Jorgehsm/SCARA_arm/robot_arm_cad/montagem_end_effector.SLDASM

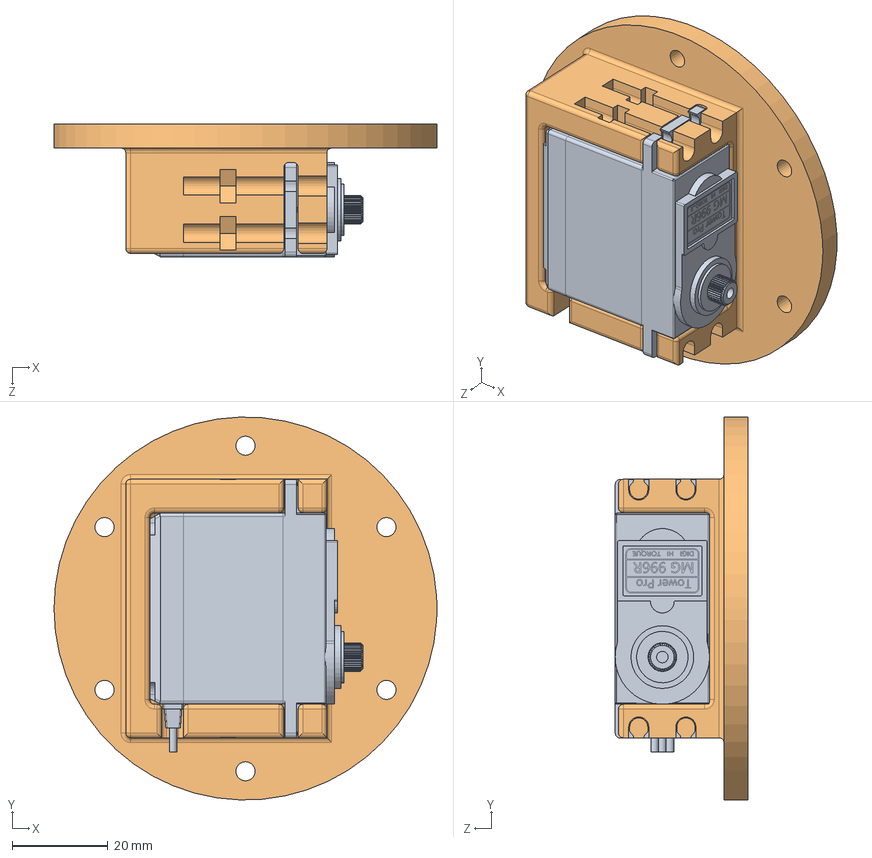
[picture p2: CAD file, 2024-11-08]
robot_arm_cad/montagem_end_effector.SLDASM
80.0 x 80.0 x 27.7 mm
junta_4_servo
servoMotorMG996R
