Jorgehsm/SCARA_arm/robot_arm_cad/garra/attachmentStraight.SLDPRT

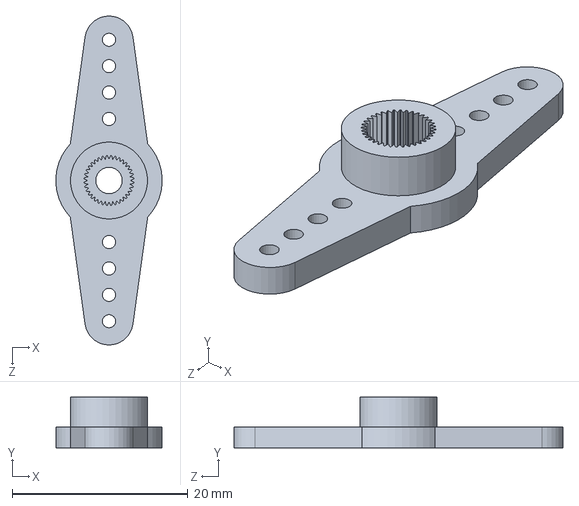
[picture p16: CAD file, 2024-09-22]
robot_arm_cad/garra/attachmentStraight.SLDPRT
12.1 x 5.75 x 37.4 mm
