Jorgehsm/SCARA_arm/robot_arm_cad/ligacao_base_eixoZ.SLDPRT

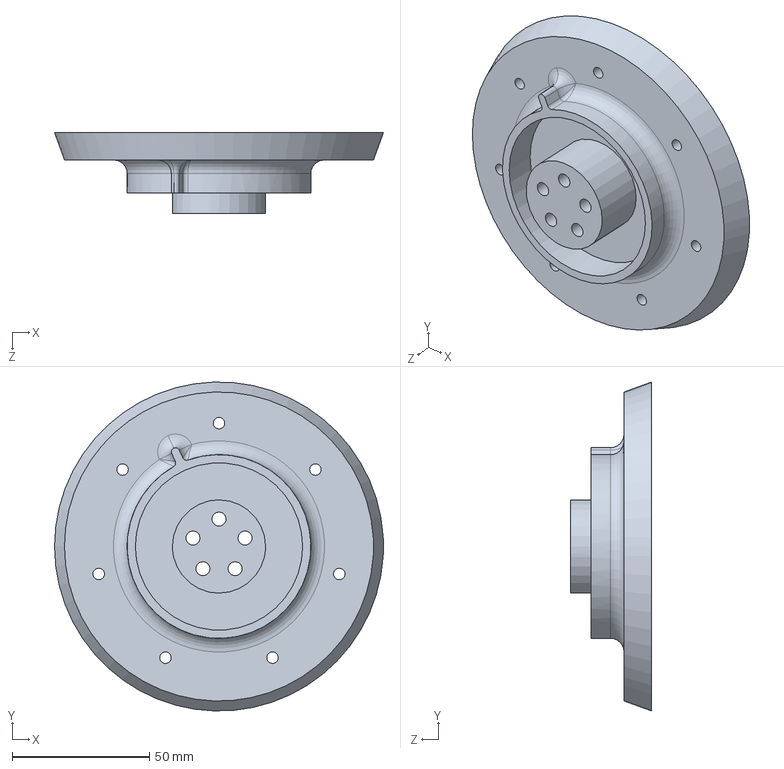
[picture p17: CAD file, 2024-09-22]
robot_arm_cad/ligacao_base_eixoZ.SLDPRT
120.0 x 119.9 x 29.5 mm
