Jorgehsm/SCARA_arm/robot_arm_cad/braco_1.SLDPRT

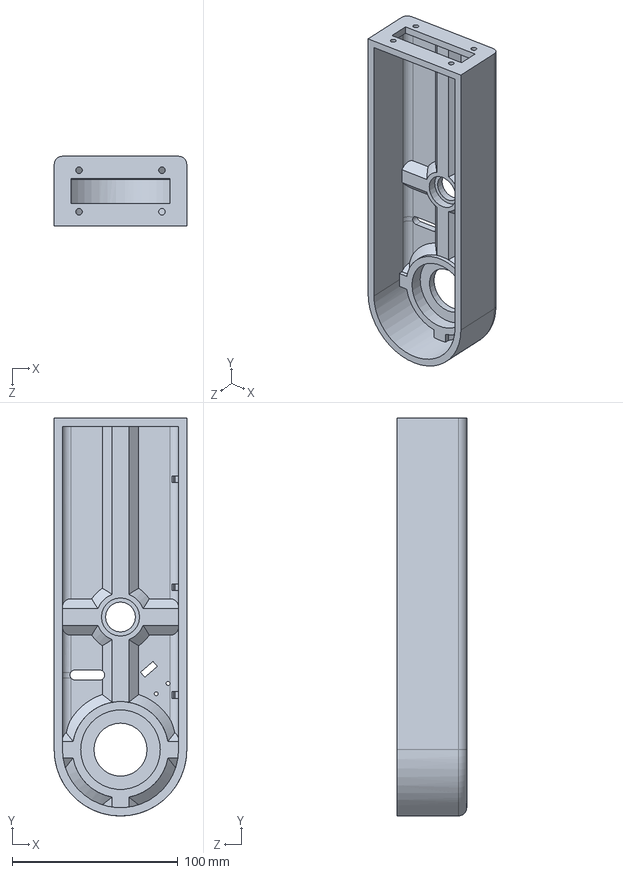
[picture p18: CAD file, 2024-09-22]
robot_arm_cad/braco_1.SLDPRT
80.0 x 240.0 x 42.0 mm
