Jorgehsm/SCARA_arm/robot_arm_cad/garra/presa.SLDPRT

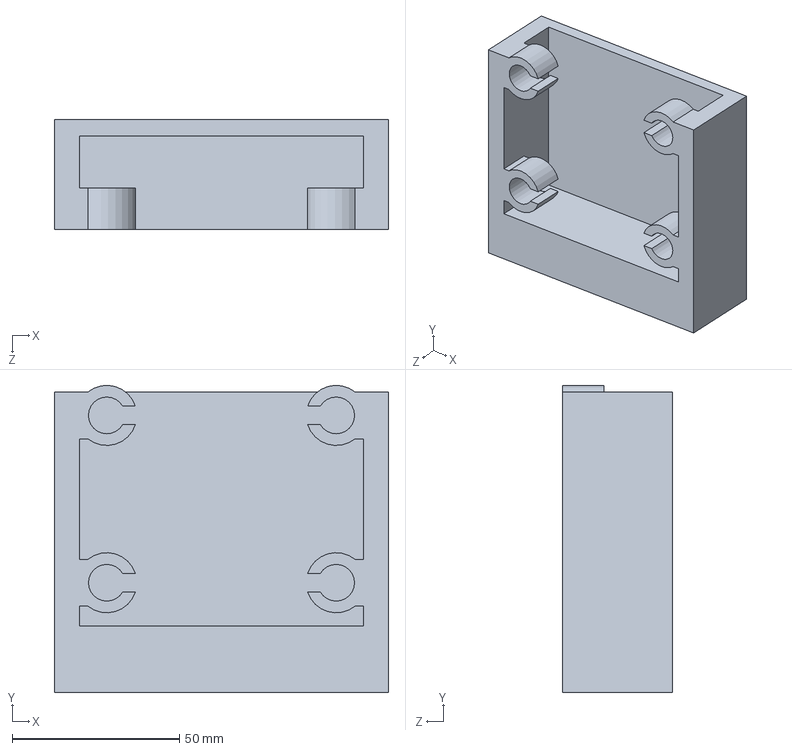
[picture p19: CAD file, 2024-09-22]
robot_arm_cad/garra/presa.SLDPRT
100.0 x 92.0 x 33.0 mm
