Jorgehsm/SCARA_arm/robot_arm_cad/garra/garra_corpo_2.SLDPRT

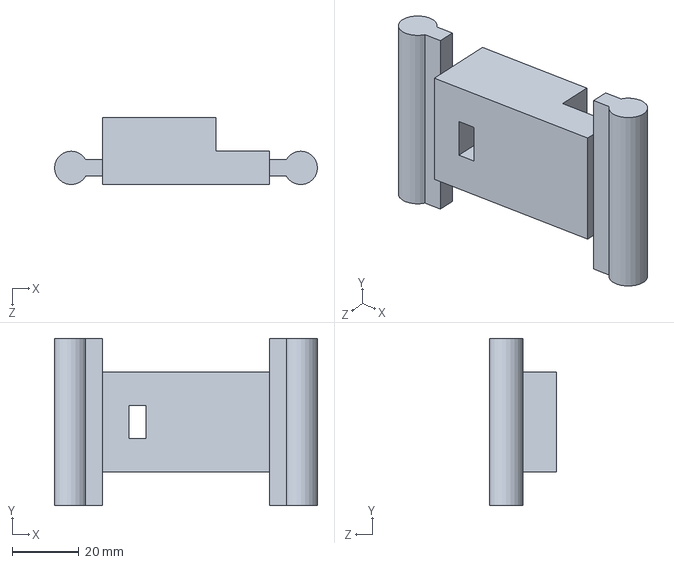
[picture p20: CAD file, 2024-09-22]
robot_arm_cad/garra/garra_corpo_2.SLDPRT
78.7 x 50.0 x 20.1 mm
