Jorgehsm/SCARA_arm/robot_arm_cad/servoMotorMG996R.SLDPRT

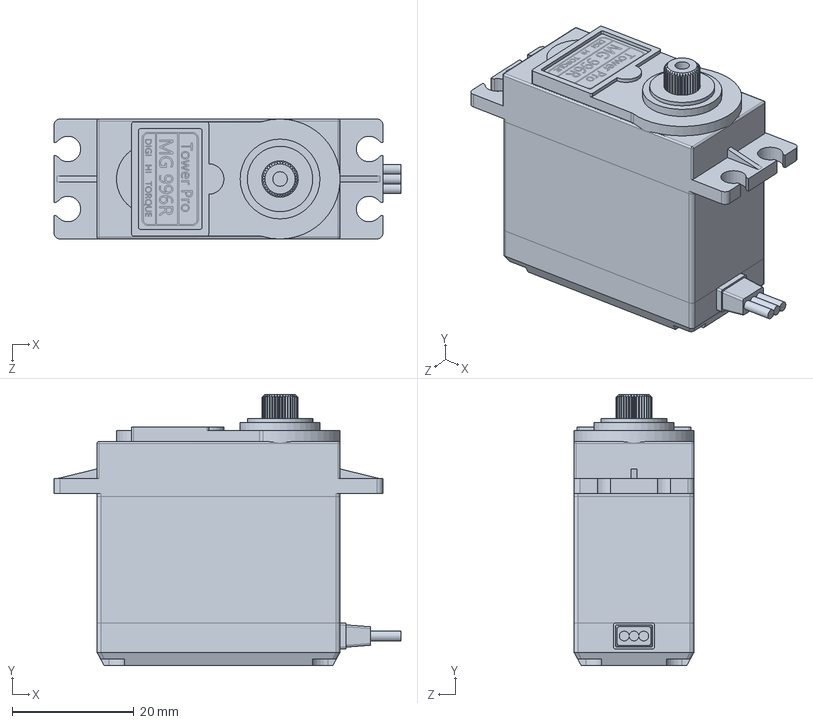
[picture p21: CAD file, 2024-09-22]
robot_arm_cad/servoMotorMG996R.SLDPRT
57.0 x 44.5 x 19.7 mm
