Jorgehsm/SCARA_arm/robot_arm_cad/suporte_eixoZ_superior.SLDPRT

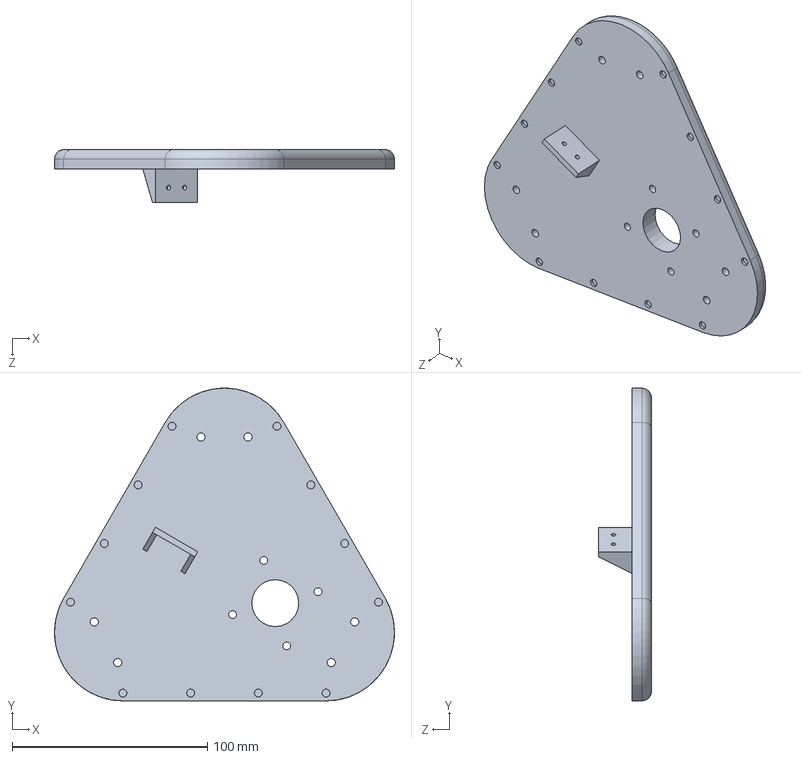
[picture p22: CAD file, 2024-09-22]
robot_arm_cad/suporte_eixoZ_superior.SLDPRT
173.9 x 160.0 x 27.2 mm
