Jorgehsm/SCARA_arm/robot_arm_cad/braco_2.SLDPRT

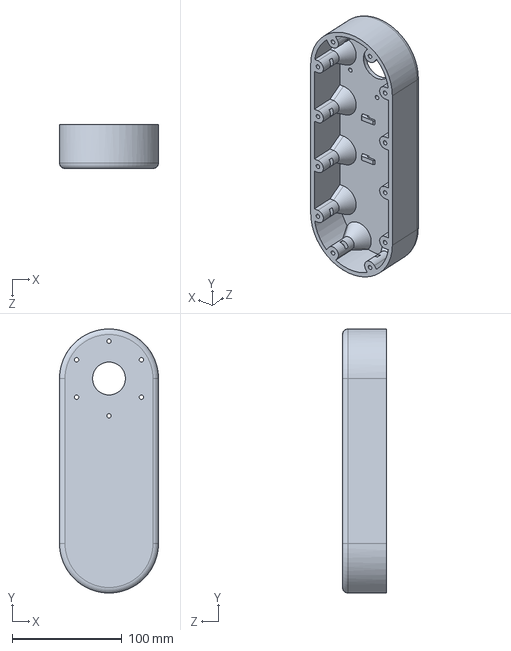
[picture p23: CAD file, 2024-09-22]
robot_arm_cad/braco_2.SLDPRT
90.0 x 240.0 x 40.0 mm
