Jorgehsm/SCARA_arm/robot_arm_cad/castanha_TR8.SLDPRT

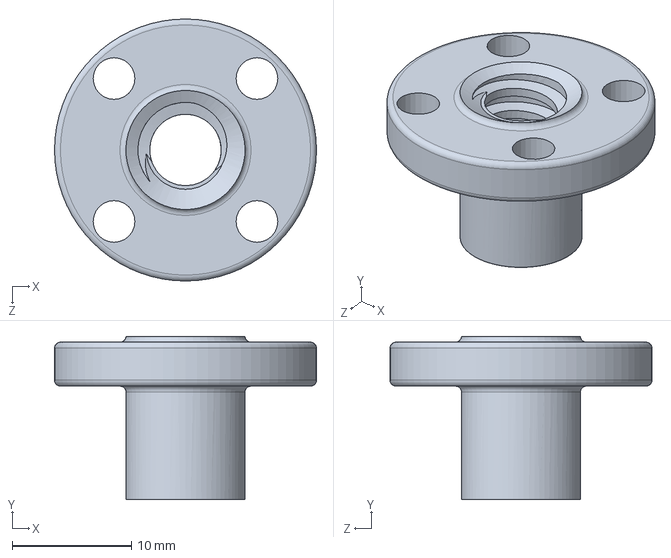
[picture p24: CAD file, 2024-09-22]
robot_arm_cad/castanha_TR8.SLDPRT
22.0 x 13.7 x 22.0 mm
