Jorgehsm/SCARA_arm/robot_arm_cad/suporte_eixoZ_base.SLDPRT

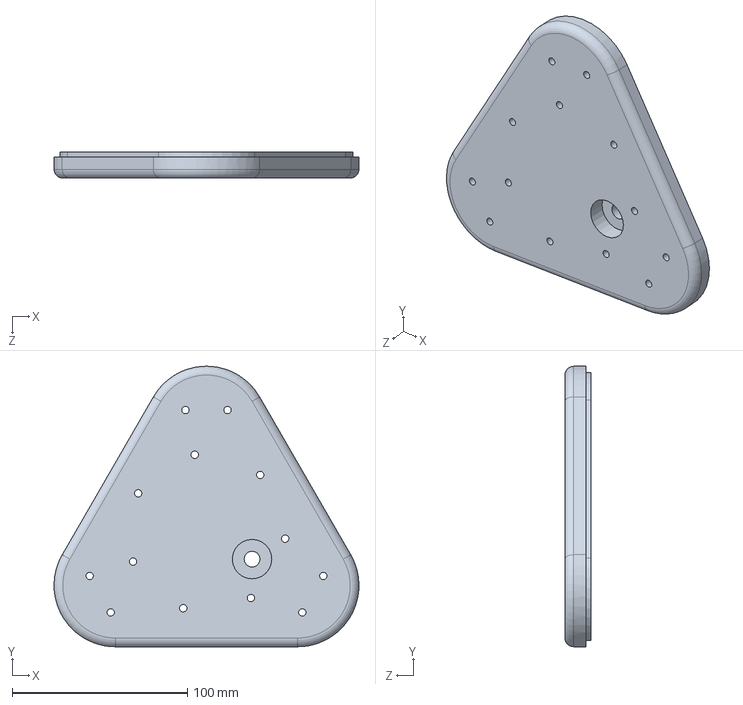
[picture p25: CAD file, 2024-09-22]
robot_arm_cad/suporte_eixoZ_base.SLDPRT
173.9 x 160.0 x 15.0 mm
