Jorgehsm/SCARA_arm/robot_arm_cad/rolamento_linear_lm8uu.SLDPRT

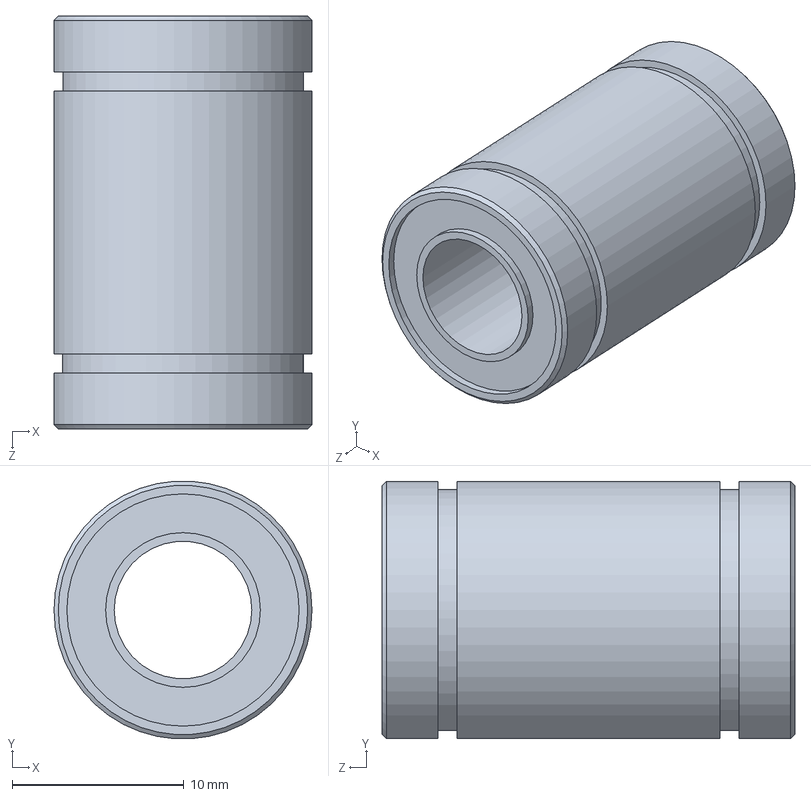
[picture p26: CAD file, 2024-09-22]
robot_arm_cad/rolamento_linear_lm8uu.SLDPRT
15.0 x 15.0 x 24.0 mm
