Jorgehsm/SCARA_arm/robot_arm_cad/suporte_eixoZ_base_tampa.SLDPRT

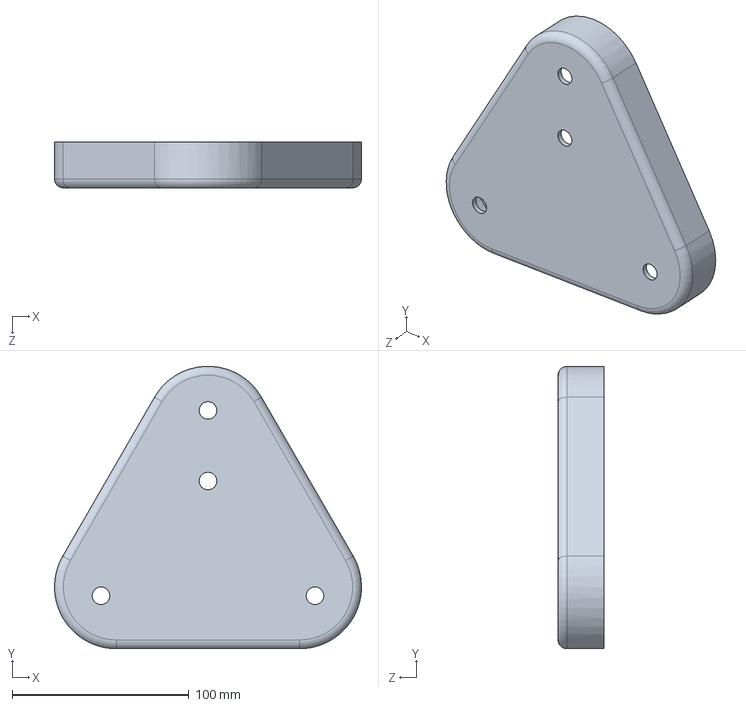
[picture p27: CAD file, 2024-09-22]
robot_arm_cad/suporte_eixoZ_base_tampa.SLDPRT
173.9 x 160.0 x 26.0 mm
