Jorgehsm/SCARA_arm/robot_arm_cad/junta_1_tampa.SLDPRT

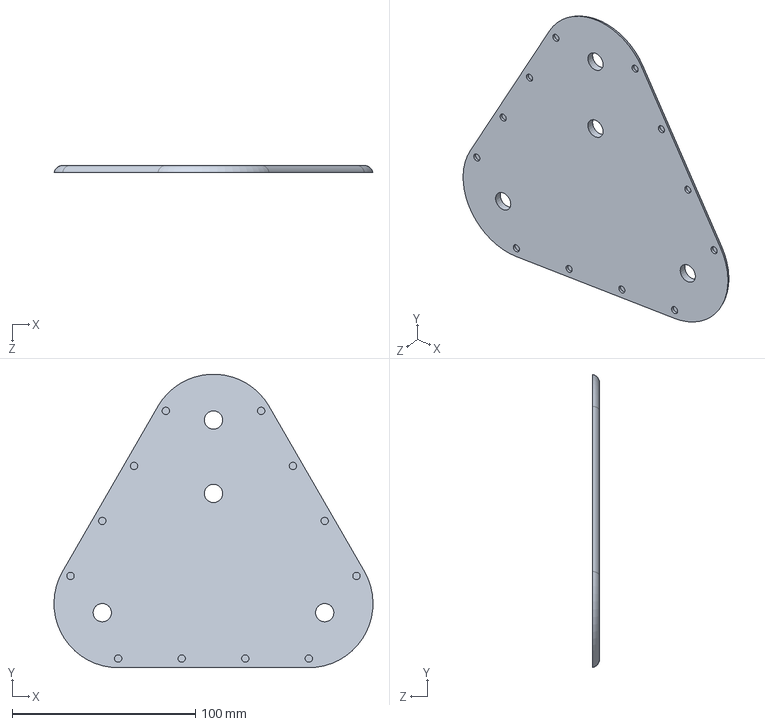
[picture p28: CAD file, 2024-09-22]
robot_arm_cad/junta_1_tampa.SLDPRT
173.9 x 159.9 x 4.00 mm
