Jorgehsm/SCARA_arm/robot_arm_cad/junta_1.SLDPRT

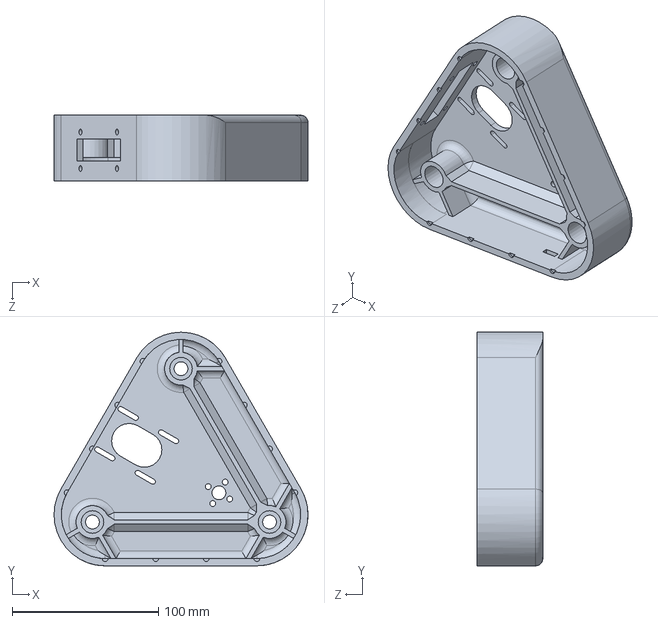
[picture p29: CAD file, 2024-09-22]
robot_arm_cad/junta_1.SLDPRT
173.9 x 160.0 x 45.0 mm
