Jorgehsm/SCARA_arm/robot_arm_cad/trava_guia_linear.SLDPRT

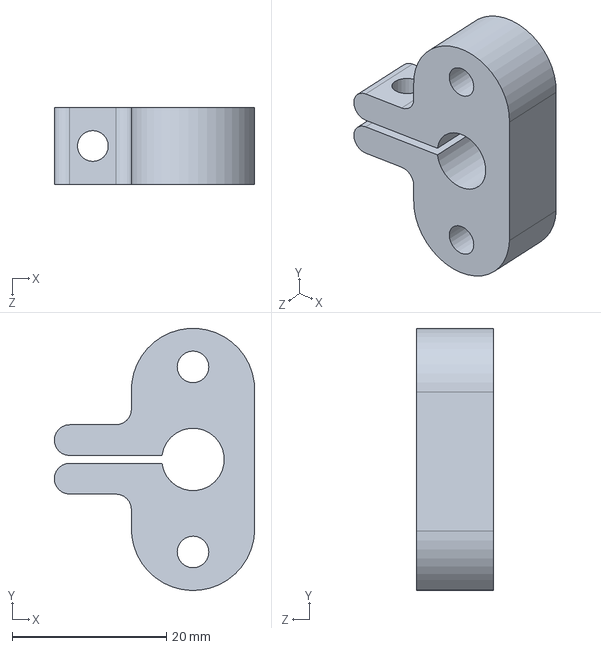
[picture p30: CAD file, 2024-09-22]
robot_arm_cad/trava_guia_linear.SLDPRT
26.0 x 34.0 x 10.0 mm
