Jorgehsm/SCARA_arm/robot_arm_cad/junta gt2-80T.SLDPRT

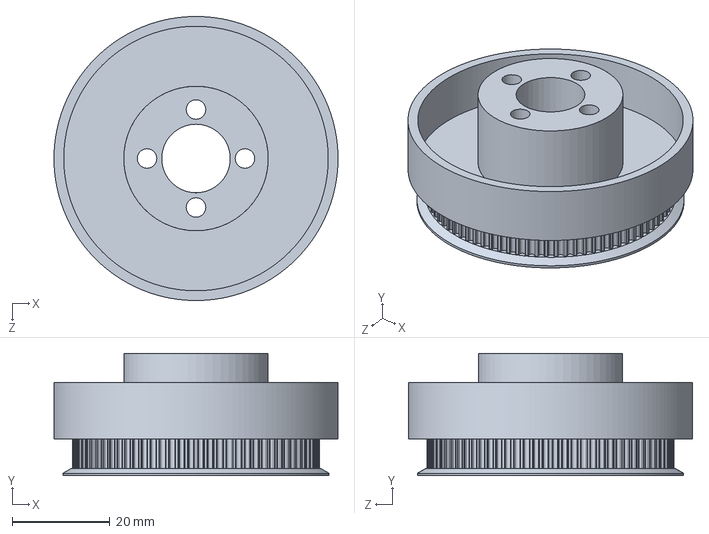
[picture p31: CAD file, 2024-09-22]
robot_arm_cad/junta gt2-80T.SLDPRT
58.0 x 25.0 x 58.0 mm
