Jorgehsm/SCARA_arm/robot_arm_cad/Nema 17.SLDPRT

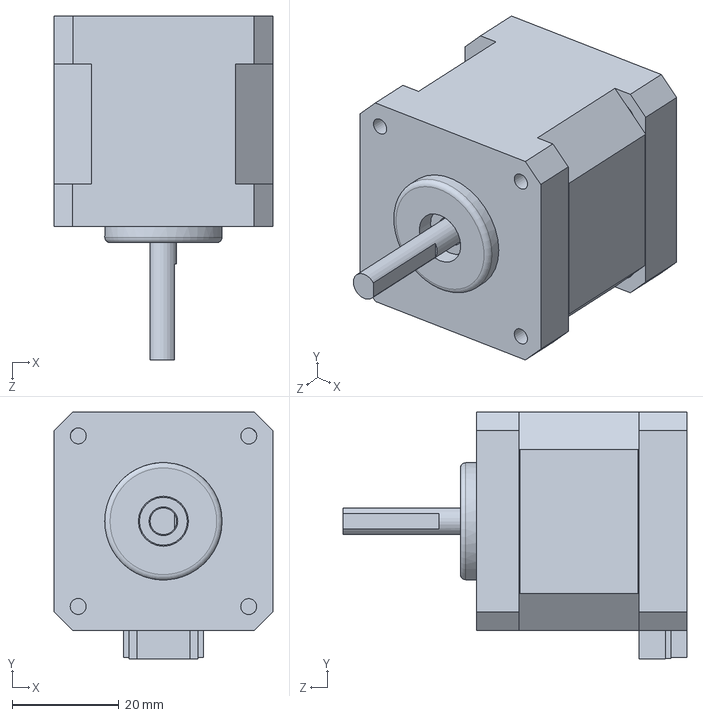
[picture p32: CAD file, 2024-09-22]
robot_arm_cad/Nema 17.SLDPRT
41.0 x 46.3 x 64.5 mm
