Jorgehsm/SCARA_arm/robot_arm_cad/guia_linear_400mm.SLDPRT

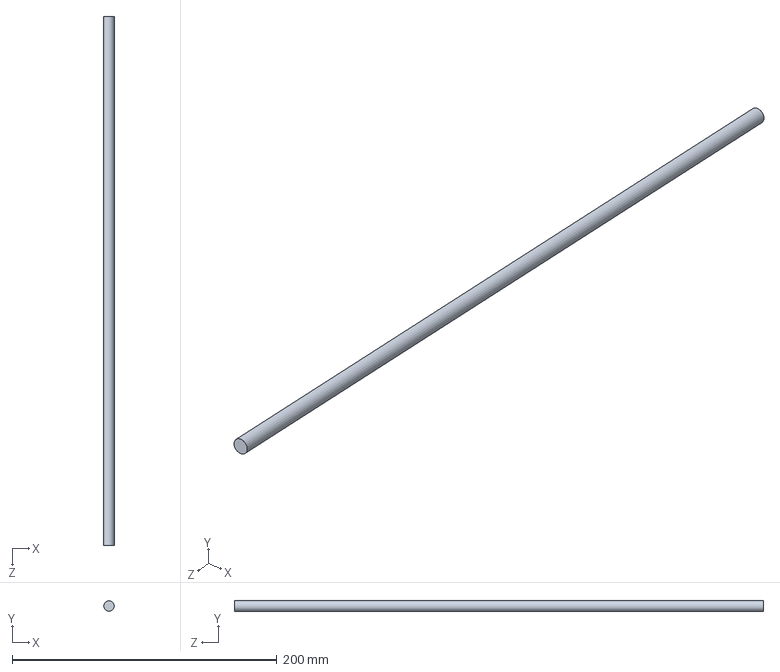
[picture p33: CAD file, 2024-09-22]
robot_arm_cad/guia_linear_400mm.SLDPRT
8.00 x 8.00 x 400.0 mm
