Jorgehsm/SCARA_arm/robot_arm_cad/base.SLDPRT

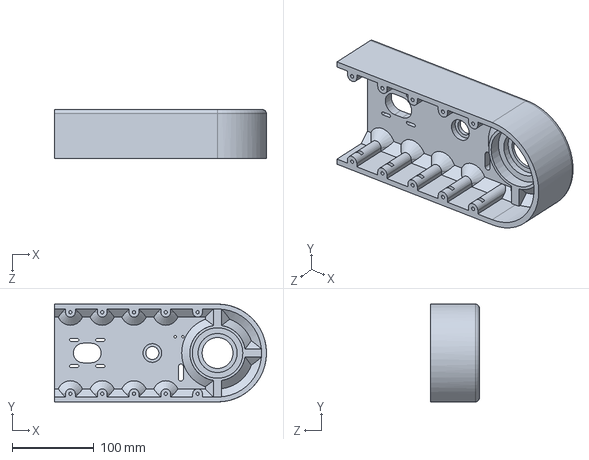
[picture p34: CAD file, 2024-09-22]
robot_arm_cad/base.SLDPRT
260.0 x 120.0 x 60.0 mm
