Jorgehsm/SCARA_arm/robot_arm_cad/junta_2.SLDPRT

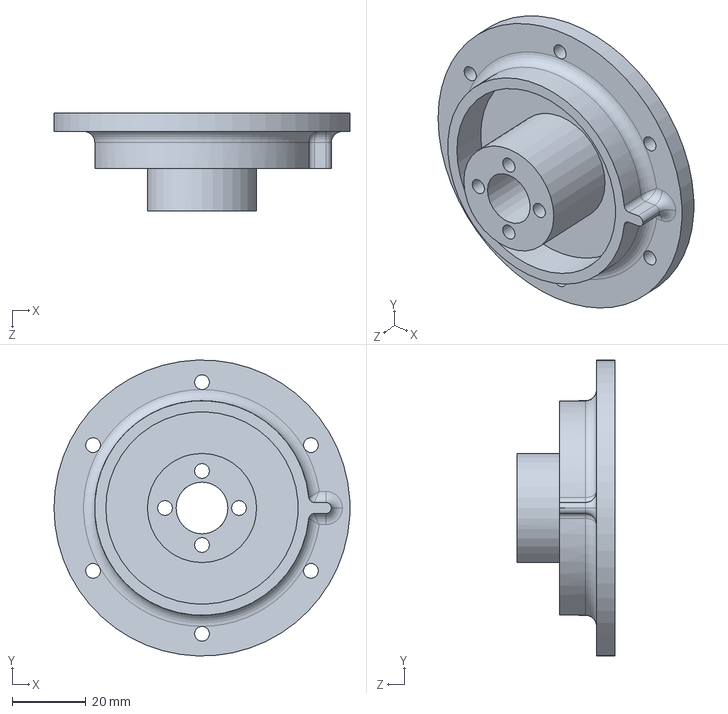
[picture p35: CAD file, 2024-09-22]
robot_arm_cad/junta_2.SLDPRT
80.0 x 80.0 x 26.5 mm
