Jorgehsm/SCARA_arm/robot_arm_cad/cover_braco_1.SLDPRT

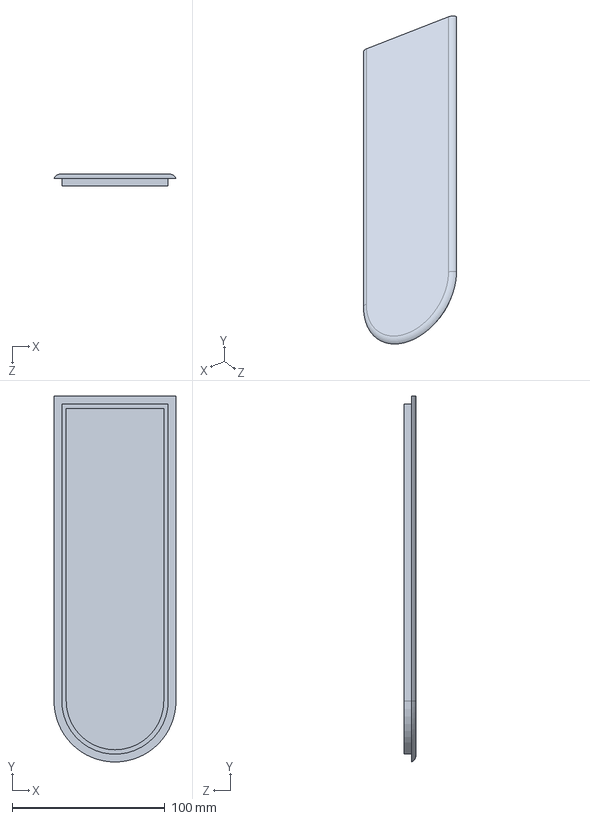
[picture p36: CAD file, 2024-09-22]
robot_arm_cad/cover_braco_1.SLDPRT
80.0 x 240.0 x 8.00 mm
