Jorgehsm/SCARA_arm/robot_arm_cad/microswitch.SLDPRT

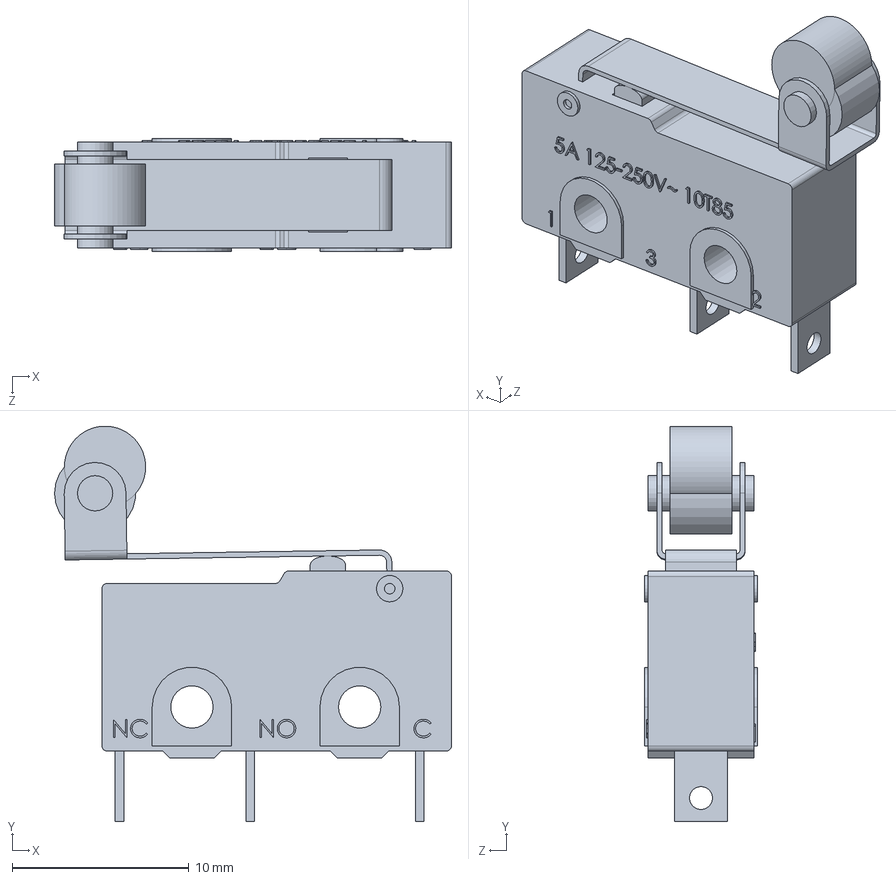
[picture p37: CAD file, 2024-09-22]
robot_arm_cad/microswitch.SLDPRT
22.5 x 22.4 x 6.40 mm
