Jorgehsm/SCARA_arm/robot_arm_cad/suporte_eixoZ_superior_tampa.SLDPRT

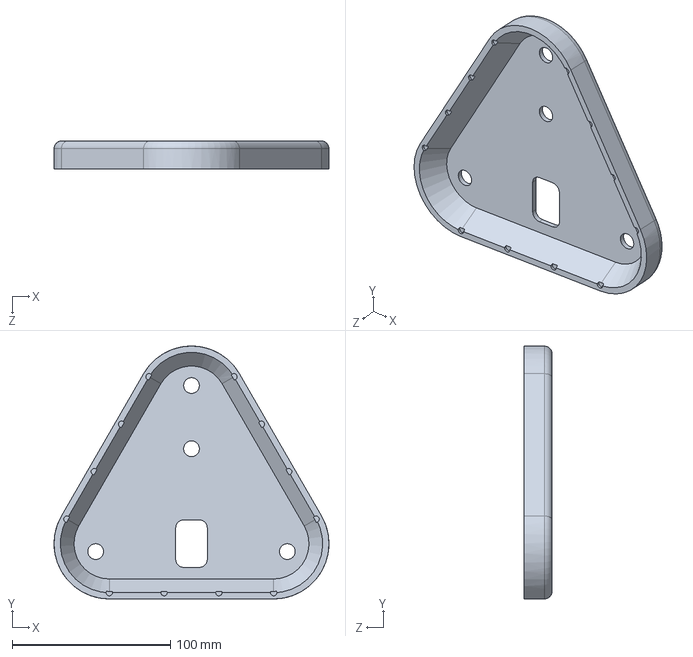
[picture p38: CAD file, 2024-09-22]
robot_arm_cad/suporte_eixoZ_superior_tampa.SLDPRT
173.9 x 160.0 x 18.0 mm
