Jorgehsm/SCARA_arm/robot_arm_cad/acoplamento_flexivel.SLDPRT

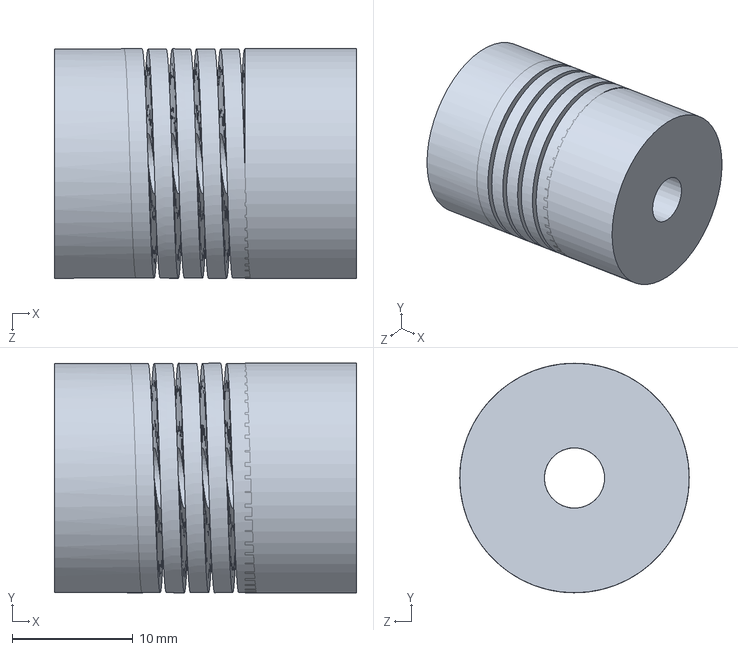
[picture p39: CAD file, 2024-09-22]
robot_arm_cad/acoplamento_flexivel.SLDPRT
25.0 x 19.0 x 19.0 mm
