Jorgehsm/SCARA_arm/robot_arm_cad/POLIA GT2 20T b5.SLDPRT

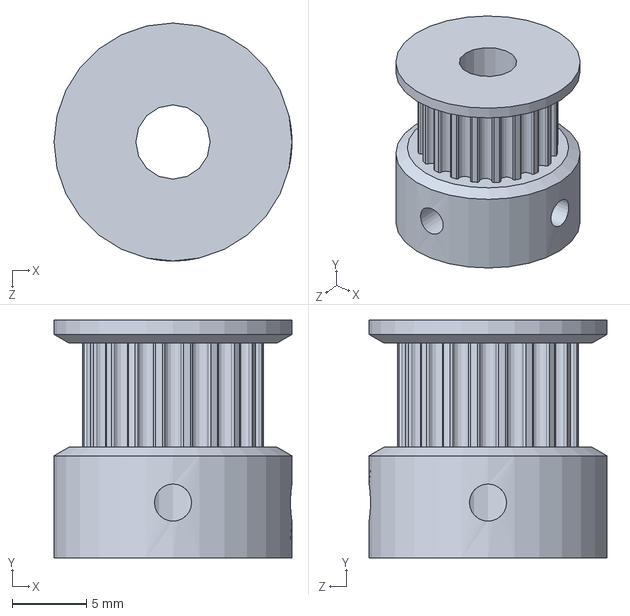
[picture p40: CAD file, 2024-09-22]
robot_arm_cad/POLIA GT2 20T b5.SLDPRT
16.0 x 16.0 x 16.0 mm
