Jorgehsm/SCARA_arm/robot_arm_cad/braco_2_inferior.SLDPRT

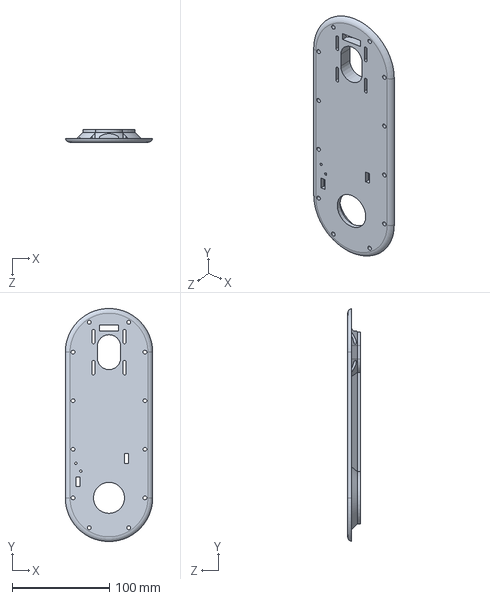
[picture p41: CAD file, 2024-09-22]
robot_arm_cad/braco_2_inferior.SLDPRT
90.0 x 239.9 x 13.0 mm
