Jorgehsm/SCARA_arm/robot_arm_cad/gt2-80T.SLDPRT

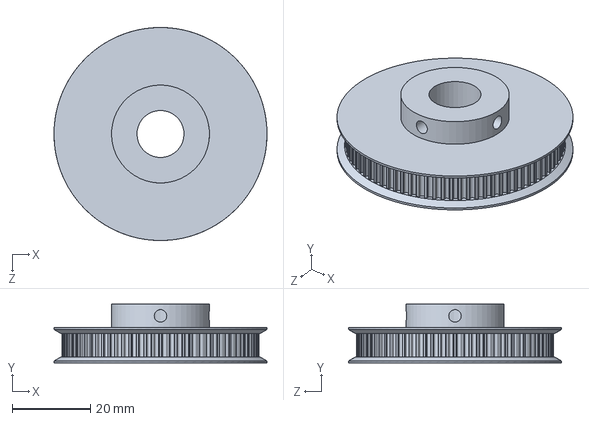
[picture p42: CAD file, 2024-09-22]
robot_arm_cad/gt2-80T.SLDPRT
54.4 x 15.0 x 54.4 mm
