Jorgehsm/SCARA_arm/robot_arm_cad/gt2-parametric-pulley.SLDPRT

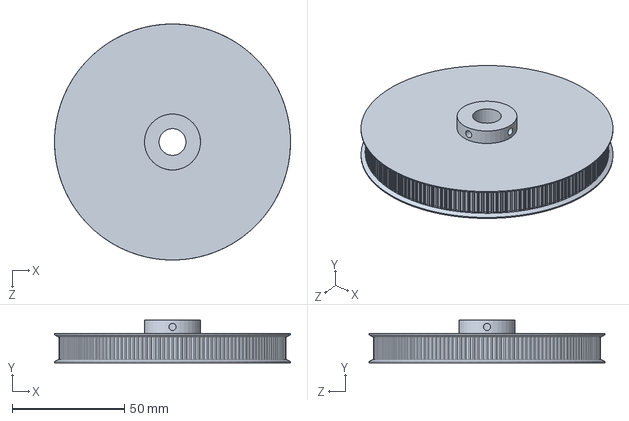
[picture p43: CAD file, 2024-09-22]
robot_arm_cad/gt2-parametric-pulley.SLDPRT
105.3 x 19.0 x 105.3 mm
